nyameaama/Converse-Engine/Avionics/SubController Program.docx

DESIGN DOCUMENT

Area : Converse Engine

Category: Feed (Piping)

TEAM: Propulsion

Nyameaama Gambrah

Sub Controller Program

Sensor Calculation

Comm Module

ECU

SPI Interrupt

Telemetry Log

Handler

SBC Program Loop

Request

Permanent Storage

Update New Value

Remove Old Value

Value Table
