nyameaama/Converse-Engine/docs/tap-off description.docx

DESIGN DOCUMENT

Area : Converse Engine

Category: Feed (Piping)

TEAM: Propulsion

Nyameaama Gambrah

Tap-Off Description

Electrical

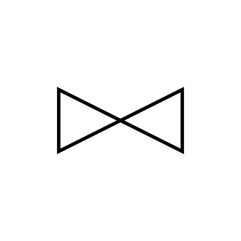
[picture p8: figure]
File:Valve.svg - Wikipedia

Tap-off propellant line

Initial Propellant Line

valve

valve

2-way pipe
