nyameaama/Converse-Engine/Avionics/Engine Startup-Shutdown (base).docx

Engine Startup (Base)

4

3

2

1

Checks

Fuel Pump Start

MOV Open

Fuel Pump Start

MFV Open

Start:

Engine Shutdown

Pumps Shutdown

Valves Close

Stop:
