nyameaama/Converse-Engine/docs/assets/rough sketches.docx

Combustion Chamber

Fuel propellant line

LOX propellant line

Injector Assembly

Engine Central Struct
