nyameaama/Converse-Engine/docs/Pressure_Fed/Engine Purge System - PF_Variant.docx

DESIGN DOCUMENT

Area : Converse Engine

Category: Feed (Purge)

TEAM: Propulsion

Nyameaama Gambrah

Engine Purge System

LOX Line

Fuel Line

C-Chamber

Electrical

Pressure loss

Valve

Pipe 2-Way

Nitrogen Gas
