nyameaama/Converse-Engine/docs/Electric_Feed/Engine Purge System-EF_Variant.docx

Engine Purge System

LOX Purge Pipe Vent

Fuel Purge Pipe Vent

C-Chamber

Valve

Post -Pump

Post -Pump

Fuel Pipe

Fuel Purge Pipe Vent

Electrical

LOX Pipe

Valve

Valve

Pre-Pump

Pre-Pump

Pressure loss

Valve

Pipe 2-Way

Nitrogen Gas

LOX Purge Pipe Vent
