nyameaama/Converse-Engine/Piping/Propellant Piping/Propellant Piping.docx

Propellant Piping

PUMP

PUMP

Inlet

Sensor Bridge

Sensor Bridge

Injector

Valve

Valve
