nyameaama/Converse-Engine/Avionics/SBControllerFirmware/PTDrivers/PT_SB-Program.docx

DESIGN DOCUMENT

Area : Converse Engine

Category: Feed (Piping)

TEAM: Propulsion

Nyameaama Gambrah

Pressure Transducer Sub Controller Program

READ IN

Controller Communication Module

ECU

Pressure Calculation

SPI Comm

GPIO

LOW

HIGH

Drivers

Digital Port
