nyameaama/Converse-Engine/Avionics/SBControllerFirmware/TCDrivers/TC_SB-Program.docx

DESIGN DOCUMENT

Area : Converse Engine

Category: Feed (Piping)

TEAM: Propulsion

Nyameaama Gambrah

Thermocouple Sub Controller Program

Digital Port

READ IN

Controller Communication Module

ECU

Temperature Calculation

SPI Comm

GPIO

LOW

HIGH

Drivers

Digital Port
