nyameaama/Converse-Engine/Avionics/SBControllerFirmware/ValveDrivers/ValveSB-Program.docx

DESIGN DOCUMENT

Area : Converse Engine

Category: Feed (Avionics)

TEAM: Propulsion

Nyameaama Gambrah

Valve Sub Controller Program

CLOSE

OPEN

Controller Communication Module

ECU

Valve State Assignment

SPI Comm

GPIO

LOW

HIGH

Drivers

Digital Port
