nyameaama/Converse-Engine/Piping/Electrical Piping/Scaled Circuit/PF_Variant/Scaled-Circuit_PF.docx

Valve Casing

Pipe-Gas (Fuel Purge)

Pipe-Gas (LOX Purge)

Power

VCC

GND

Thermocouple Casing

Signal-In

Pipe-Electrical

Pipe-Electrical

Relay Module

Nitrogen Gas

Pressure Transducer Casing

Oxidizer Inlet

Pressure Transducer Casing

Power

GND

VCC

Signal-In

Relay Module

3

Pipe-Electrical

Pipe-Electrical

Valve Casing

Valve Casing

3

Pipe-Propellant-Line

4

4

Power

GND

VCC

Signal-In

Relay Module

Pipe-Electrical

CLK

VCC

CS

DO

AD595 Thermocouple Amplifier

Thermocouple Casing

Pipe-Electrical

ECU Power Supply Assembly

VCC

Pipe-Electrical

CS

DO

CLK

ECU

AD595 Thermocouple Amplifier

Fuel Inlet

Pipe-Propellant-Line

Pressurizer
