nyameaama/Converse-Engine/Nozzle-CC/misc_docs/Ariel_TCA_Calculations.pdf

# Rocket Propulsion Laboratory: Ariel Thrust Chamber Assembly Calculations Draft

### M. Phalen, R. Libman, J. Villegas

### March 5, 2017

Chief Engineer | Date

Abstract

This document covers the design of the combustion chamber and nozzle of RPL’s 500lbf methalox engine, Ariel, with an 80% bell nozzle approximation. Note: Gas Pressures are reported in atmospheres for easy comparison to curves sourced from braeunig.com. Future iterations of this document will be translated to English units as is common in for aerospace literature.

Nomenclature
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
m˙ F
m˙ O

= Chamber Area (in²
)
= Nozzle Exit Area (in²
)
= Nozzle Throat Area (in²
)
= Chamber Diameter (in)
= Nozzle Exit Diameter (in) = Nozzle Throat Diameter (in) = Characteristic Velocity ( f t
s

)
= Thrust Coefficient (unitless)
= Characteristic Length (in) = Length necessary for complete combustion. = Chamber Length (in)
= Thurst (lbf )
= Factor of Safety (Unitless)
= Gravity of Earth ( f t
s

2 )
= Specific Impulse (s)
= Ambient Pressure (atm)
= Chamber Pressure, (atm)
= Exit Pressure (atm)
= Nozzle Throat Pressure, (atm)
= Universal Gas Constant, ( lb∗lbf
◦R∗lb−mol)
= Yield Stress of Chamber Lining (psi) = Chamber Temperature (◦R)
= Nozzle Throat Temperature (◦R)
= Chamber Wall Thickness (in)
= Chamber Volume (in³
)
= Propellant Mass Flow Rate (lb
s

)
= Fuel Mass Flow Rate (lb
s

)
= Oxidizer Mass Flow Rate(lb
s

)
Mr
Mw
c
e
γ

= Mixture Ratio (unitless)
= Molecular Weight of the Exhaust (amu)
= Contraction Area Ratio (unitless)
= Expansion Area Ratio (unitless)
= Adiabatic Index-Ratio of Specific Heats (unitless)

Constants

FoS
ge
Pa
R
Sy

= 1.4
= 32.1740 f t
s

2
= 1 atm
= 1545.348963 lb∗lbf ◦R∗lb−mol

= 80000 psi

## 1 Introduction

Compared to other traditional rocket propellants, LOX and liquid CH4 is advantageous for deep space missions for several reasons. While it has a lower specific vacuum impulse than LOX/LH2, it presents other favorable properties such as a higher boiling point. This requires a less severe temperature differential to be maintained, reducing the risk of boil off. Methalox’s density is also significantly higher than LOX/LH2, allowing for smaller-less massive-propellant tanks. Further more, the propellant required for an additional trip(s) from an carbon dioxide rich atmosphere can be produced on-site with a small amount of seed hydrogen, allowing for considerable weight-propellant savings important for mission design. Here the Rocket Propulsion Laboratory goes through the initial design of a 2000 lbf methalox engine, dubbed Ariel.

## 2 Approach

To ensure accuracy and reliability in the calculations, several reference texts were used to baseline the design. In particular, Modern Engineering for Design of Liquid-Propellant Engines by Dieter K. Huzel and David H. Huang and Rocket Propulsion Elements, 8

th Ed.
by George P. Sutton were heavily referenced to bridge the knowledge gap and guide the designs of the combustion chamber and the nozzle.
Both texts show that the overall design of a given thrust chamber assembly is character-ized by the desired propellant, chamber pressure, exit pressure, thrust, and nozzle contour for a given engine. From a given propellant and chamber pressure, key parameters of the engine’s exhaust can be computed. In particular they are: the adiabatic index, adiabatic flame temperature, molecular weight of the exit gas, and the optimum mixture ratio of the propellant. However neither text goes into detail about characterizing the chemical properties of propellants. For this, software like Stanford’s StanJan and NASA’s CEA application are used. braeunig.us hosts the relevant curves for methalox, calculated with StanJan . This data was cross checked with CEAweb to verify accuracy.

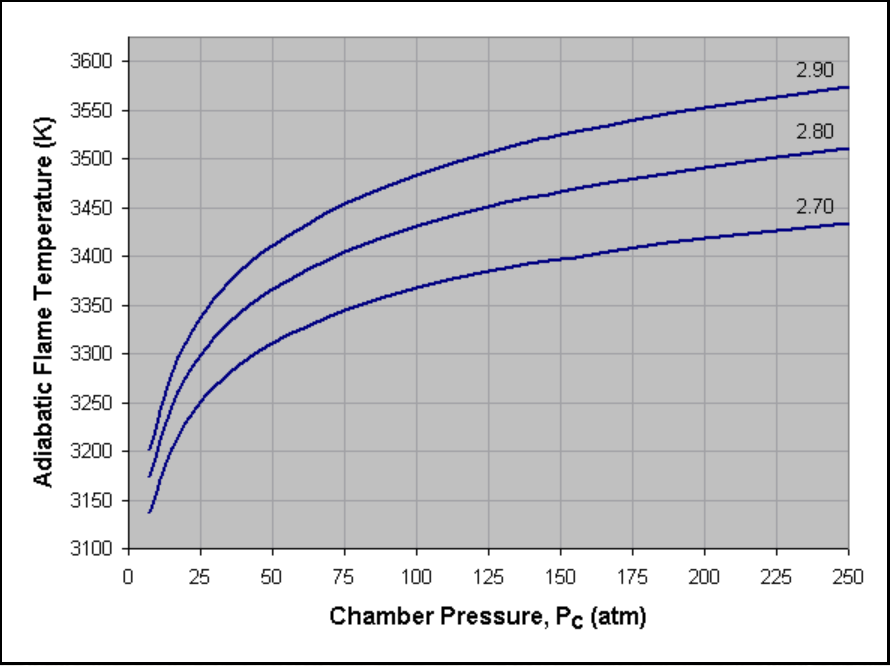
[picture p12: figure]
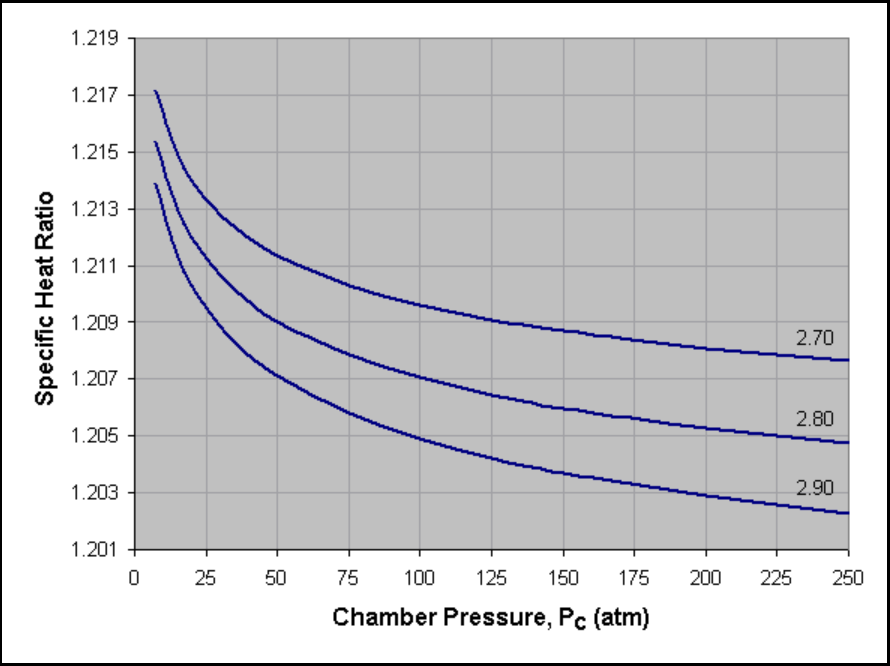
[picture p13: figure]
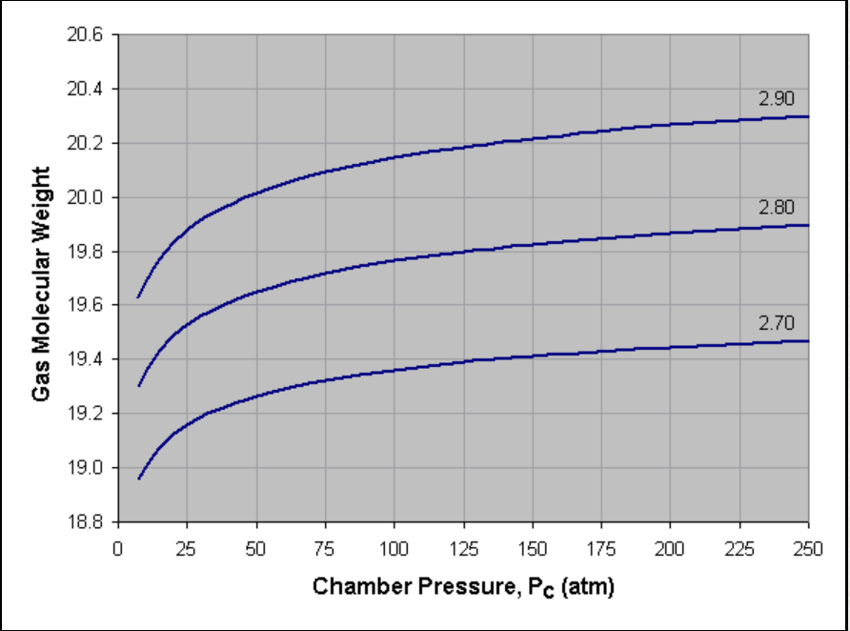
[picture p14: figure]

(a) Adiabatic Flame Temp. | (b) Molecular Weight of Gas | (c) Specific Heat Ratio

Figure 1: Three Data-sets in Reference

Determining the optimum mixture ratio requires that Specific Impulse vs Mixture Ratio curves be calculated, holding Chamber Pressure constant. The global maxima for these curves provide the optimal mixture ratio for a given pressure. This is shown in another graph from braeunig.us , where they have graphed Optimal Mixture Ratio vs Pressure, holding Exit Pressure constant:

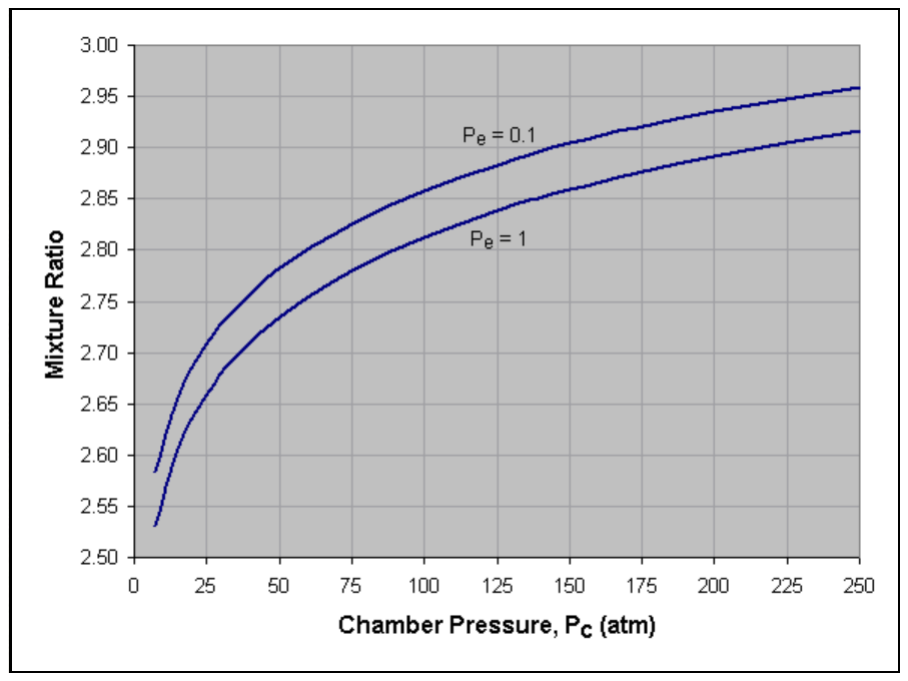
[picture p15: figure]

Figure 2: MR versus Pc

### 2.1 Thrust

The desired thrust acts as an indirect scaling factor for the engine, influencing the diameter of the chamber and diameter of the nozzle’s exit relative to the diameter of the nozzle’s throat. With this in mind, Ariel was designed to produce only 500lbf as this would reduce the cost in both materials and time to produce as well as mitigate risks that would scale with the engine size.

### 2.2 Nozzle Contour

The nozzle follows suit in that an an 80% bell nozzle approximation is used as it provides a reasonable trade off between performance and weight. Furthermore, considering how thor-oughly bell nozzles have been studied and documented, they are a safe choice for RPL’s first attempt at constructing a liquid rocket engine.

### 2.3 Exit Pressure

As [citation needed, Huzel+Huang] explains, having an exit pressure different from the ambient pressure results in over or under expansion of the exhaust which are both unfavorable. Ariel was designed to be fired at sea level, so the desired Exit Pressure was defined as one atm.

### 2.4 Chamber Pressure

Looking at Figure 1 and Figure 2 and Equations ?? and ??, it’s apparent that a higher chamber pressure and corresponding mixture ratio would result in higher specific impulse. However, given that Ariel will be a small motor and a first for RPL, high pressures were considered an unnecessary safety risk. At the other end of the spectrum, while lowering chamber pressure mitigates pressure related hazards, minor fluctuations in the mixture ratio would result in increasing large perturbations of chamber pressure. With this in mind, looking at Figure 2 it can be seen that a reasonable range for chamber pressure is 50 to 90 atmospheres.
Ariel was designed to have a chamber pressure of 68 atmospheres. 68 is a conservative average, it falls in the middle of the above range but leans slightly towards the lower end.

### 2.5 Exhaust Properties

With the characteristic engine parameters defined, exhaust properties can discerned from the data generated from StanJan or CEAweb.

## 3 Calculations

### 3.1 Characteristic Engine Parameters

Having defined the independent characteristic parameters for Ariel’s combustion chamber the optimal mixture ratio of methalox to feed the engine was approximated by examining Figure 2. Using these values for thrust, chamber pressure, exit pressure, and the mixture ratio the exhaust parameters where calculated with CEAweb ??

Characteristic Engine Parameters F
Pc
Pe
Tc
Mr
Mw
γ

= 2000 lbf
= 68 atm (999.321 psi)
= 1 atm (14.6959 psi)
= 6051.60 ◦R
= 2.77
= 20.158 amu
= 1.2161

### 3.2 Area Contraction and Expansion Ratios, c and e

c =

Ac
At

= 1.317303 +

32346880 − 1.317303
1 + ( Dt
1.041567∗10⁻¹⁰ )
0.6774809 = 6.0510 | (1)

This equation for the contraction area ratio comes from a rough fitting of Figure 4-9 from Huzel and Huang .

e =

Ae
At

=

(

2
γ+1 )

1
γ−1 (

Pc
Pe

)

1
γ

[( γ+1
γ−1

)[1 − (

Pe
Pc

)

γ−1
γ ]] ¹
2
= 8.5917 | (2)

### 3.3 Thrust-Chamber Performance Parameters

### 3.3.1 Characteristic Velocity, c∗

c

∗ =

√
geγRTc

γ

rh
2

γ+1 i γ+1
γ−1

= 5929

f t
s

(3)

Characteristic Velocity is a measure of the combustion performance, similar to Specific Impulse.

### 3.3.2 Thrust Coefficient, Cf

Cf = λ ∗

### vuut

2γ

2
γ − 1
2

γ + 1 γ+1
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
Pe − Pa
Pc
= 1.5640 | (4)

Where λ = .985 is the correction factor associated with a 80% bell nozzle for an engine of this size . It applies only to the momentum term of Cf as it accounts for divergence from uniform axial flow (the contour of the nozzle at it’s exit isn’t parallel to the central axis of the thrust chamber).

### 3.3.3 Specific Impulse, Isp

Isp =

c

∗Cf
ge
= 288s | (5)

Specific Impulse is the amount of thrust generated per unit of propellant, or, in essence, the performance of our engine.

### 3.4 Mass Flow, m˙

The Propellant Mass Flow Rate

m˙ =

F

Isp

= 6.9394

lb
s

(6)

the Fuel Mass Flow Rate,

m˙ F =

m˙
r + 1

= 1.841

lb
s

and the Oxygen Mass Flow Rate.

m˙ O =

r ∗ w˙
r + 1

= 5.099

lb
s

### 3.5 Nozzle Throat Parameters

Nozzle Throat Temperature,

Tt = Tc

2
1 + γ
= 5461.5
◦R | (7)

Nozzle Throat Pressure,

Pt = Pc

γ + 1
2

−γ
γ−1
= 38.173atm | (8)

Nozzle Throat Area,

At =

mI ˙ sp
PcCf

= 1.2796in²
(9)

and Nozzle Throat Diameter.

Dt =

4At
π

1
2
= 1.2764in | (10)

Nozzle Exit Area,

Ae = eAt = 10.9942in²
(11)

and Nozzle Exit Diameter.

De =

4Ae
π

1
2
= 3.7414in | (12)

### 3.6 Chamber Dimensions

a) Calculate the Chamber Volume.

Vc = AtL

∗ = 51.1848in³
(13)

L

∗ = 40in

Characteristic Lengths and Volumes are a more intuitive way to express the requirements for efficient combustion of the propellant, which is usally expressed as propellant stay time (τ ). Characteristic Length is proportional to the complexity molecules that make up the propellant; examining table from Huzel and Huang, it can be reasoned Methalox will have a characteristic length between that of RP-1 and LOX+LH2. This is estimated to be 40 in.
b) Calculate the Chamber Length by utilizing the contraction ratio (c) to solve
for Ac, and thus Dc.

Vc = (1.1)Ac ∗ Lc = 51.1848in³ (14)

Chamber Area
Ac = cAt = 7.7429in²
(15)

Chamber Diameter

Dc = (⁴Ac
π

)

1
2 = 3.1398in | (16)

Chamber Length

Lc =

Vc
1.1Ac
= 6.0096in | (17)
c) Chamber Wall Thickness

From Barlow’s law relating the maximum working pressure to a pipe’s geometry:

FoS ∗ Pc =

2 ∗ Sy ∗ tw

Doutside

(18)

Where Doutside = Dc + 2tw

We derived the equation that gives the desired thickness of the chamber lining

tw =

FoS ∗ Pc ∗ Dc
2 ∗ Sy − 2 ∗ FoS ∗ Pc
= 0.0279in | (19)

Sy equals the yield stress of material used for the chamber lining; for Ariel that

material is Inconel 718, with a yield stress of 80000 psi

### 3.7 Nozzle Contour

Most references suggest using a parabolic approximation for bell nozzles . However, the examples provided in Huzel and Huang couldn’t be reconciled with the data they provided. A lecture from Georgia Tech suggested to use the general conic equation to approximate the contour of a bell nozzle. This follows the form:

y = P ∗ x + Q + (S ∗ x + T)

1
2 | (20)

## 4 Results

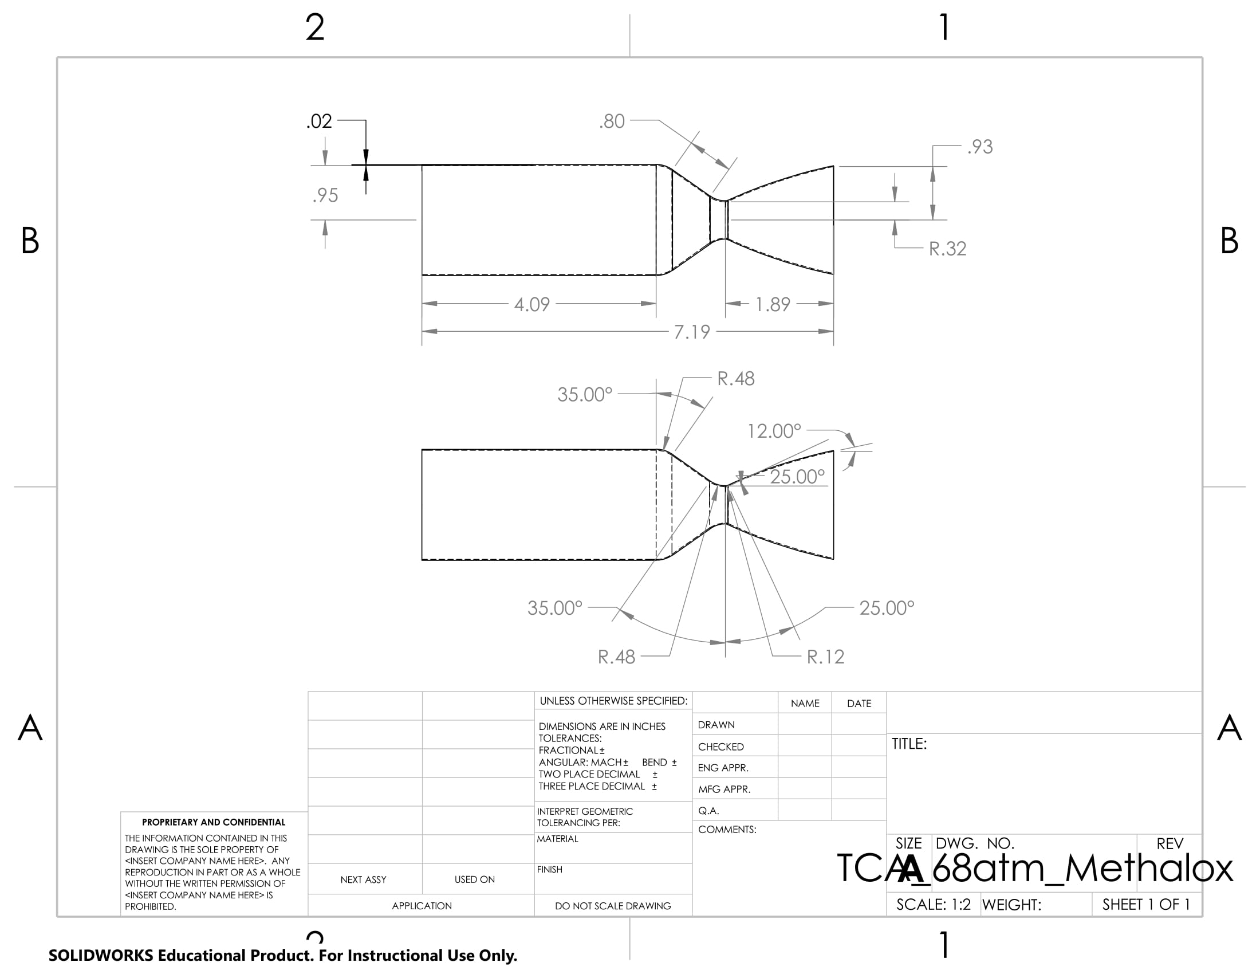
[picture p16: figure]

Figure 3: Current Model

## 5 Conclusions

In order to bridge the knowledge gap between professional industry knowledge and collegiate student knowledge, we have heavily utilized the information from Modern Engineering for Design of Liquid-Propellant Engines by Dieter K. Huzel and David H. Huang as well as Rocket Propulsion Elements, 8th Ed. by George P. Sutton . This literature provided us with the equations necessary to design and model the first iteration of Ariel. Further iteration will be guided by results from analysis, as an example, CFD can be used to test the approximation made for c.
