nyameaama/Converse-Engine/docs/PLACEMENT.docx

DESIGN DOCUMENT

Area : Converse Engine

Category: Feed (Struct)

TEAM: Propulsion

Nyameaama Gambrah

COMPONENT PLACEMENT

Face 2

Face 4

Face 3

Face 1

s

Faces = 4
