nyameaama/Converse-Engine/Avionics/Peripheral Controllers Abstract.docx

DESIGN DOCUMENT

Area : Converse Engine

Category: Feed (Avionics)

TEAM: Propulsion

Nyameaama Gambrah
