nyameaama/Converse-Engine/Nozzle-CC/igniter/Igniter (Abstracted).docx

Igniter (Abstracted)

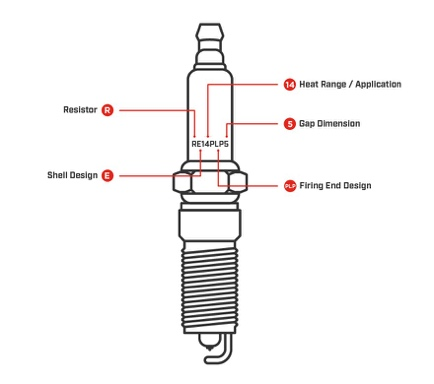
[picture p17: figure]
What are the parts of a spark plug called? | Champion Auto Parts

Spark Plug
