nyameaama/Converse-Engine/Avionics/Casings/EngineControlUnit/ECU/ECU-Casing.png

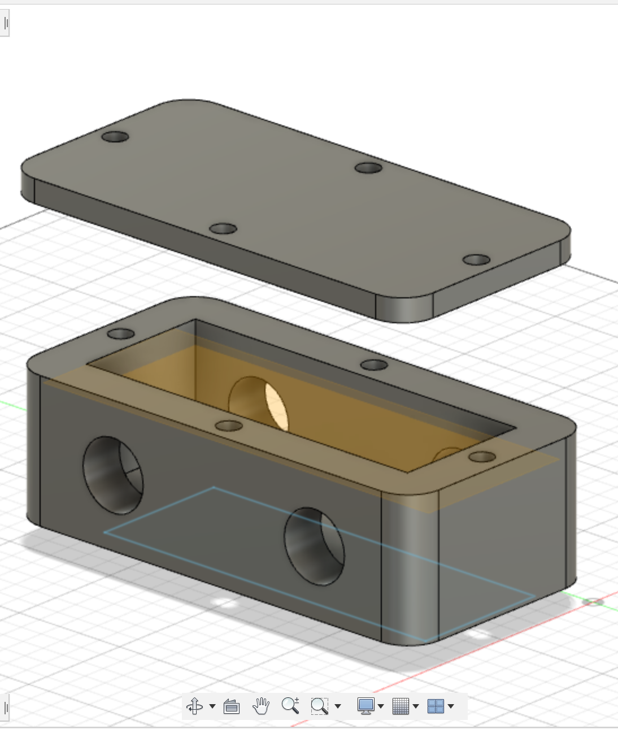
Avionics/Casings/EngineControlUnit/ECU/ECU-Casing.png
