nyameaama/Converse-Engine/Nozzle-CC/injector/injector-assembly.png

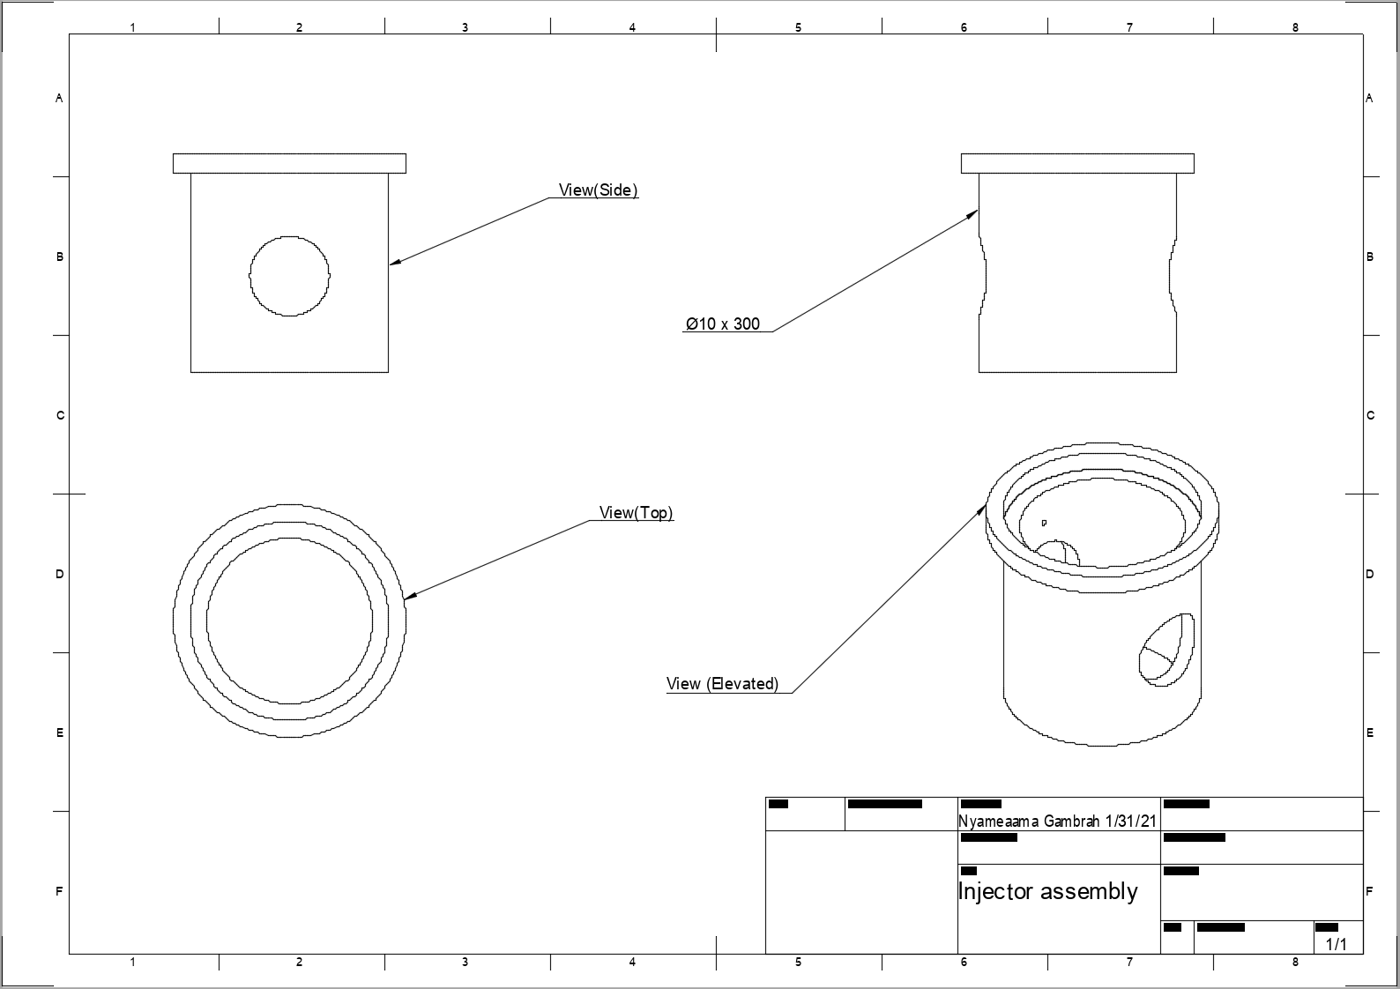
Nozzle-CC/injector/injector-assembly.png
