nyameaama/Converse-Engine/docs/Controller-Power-Assemblies/measure-1.png

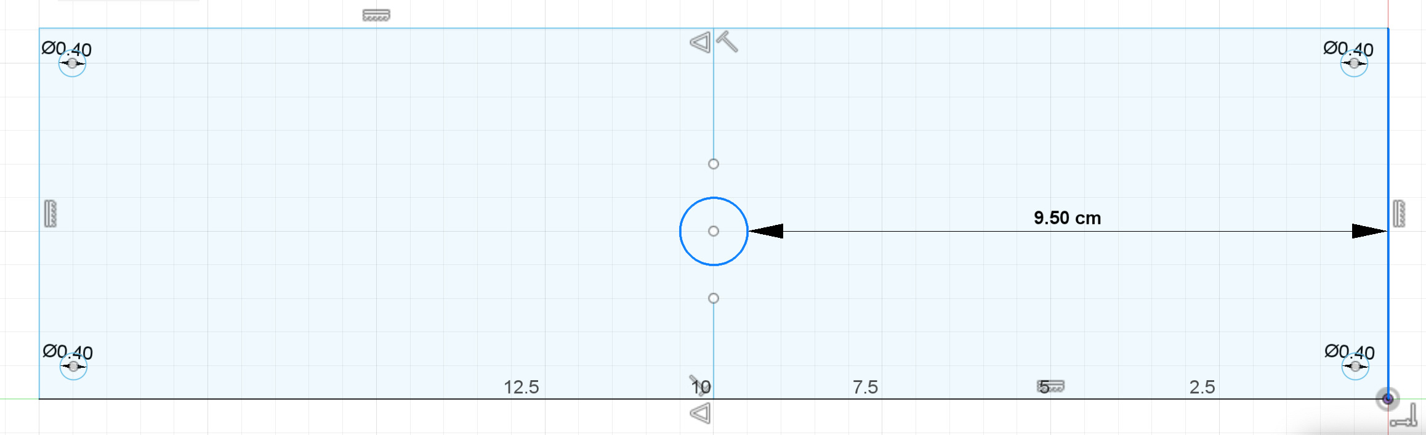
docs/Controller-Power-Assemblies/measure-1.png
