nyameaama/Converse-Engine/docs/Testing-terminal-controller/Casing/arduino-uno-in-fusion-360-format-1/Capture.PNG

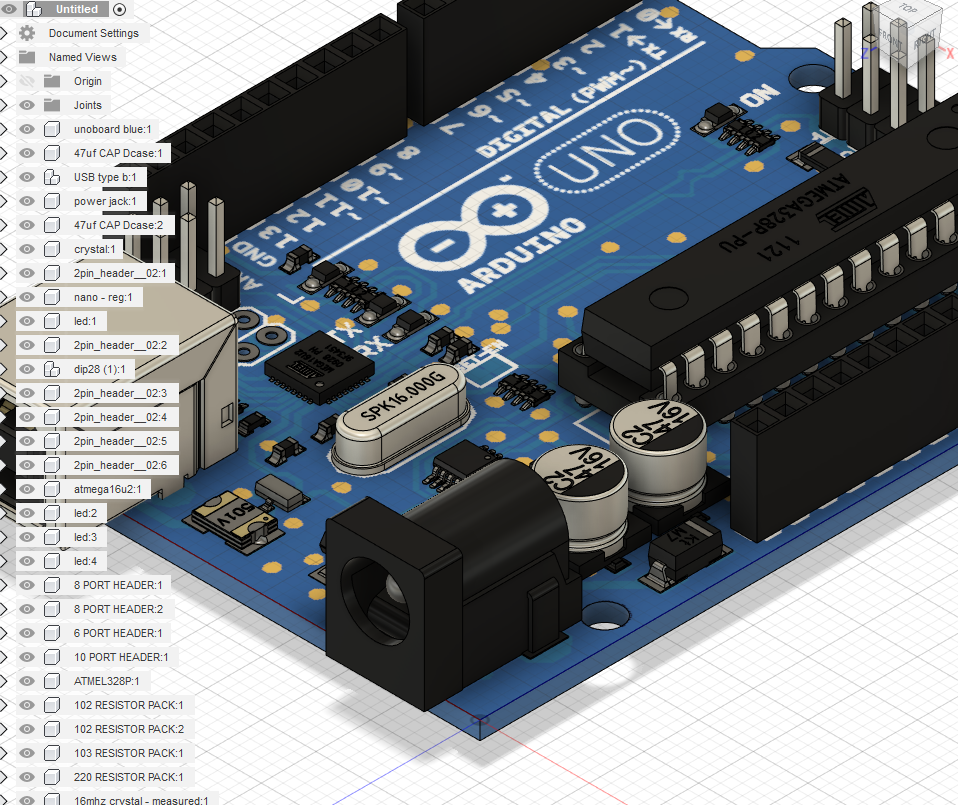
docs/Testing-terminal-controller/Casing/arduino-uno-in-fusion-360-format-1/Capture.PNG
