nyameaama/Converse-Engine/docs/Testing-terminal-controller/Casing/arduino-uno-in-fusion-360-format-1/raas-rendering20150623-6149-15dbs3x.jpg

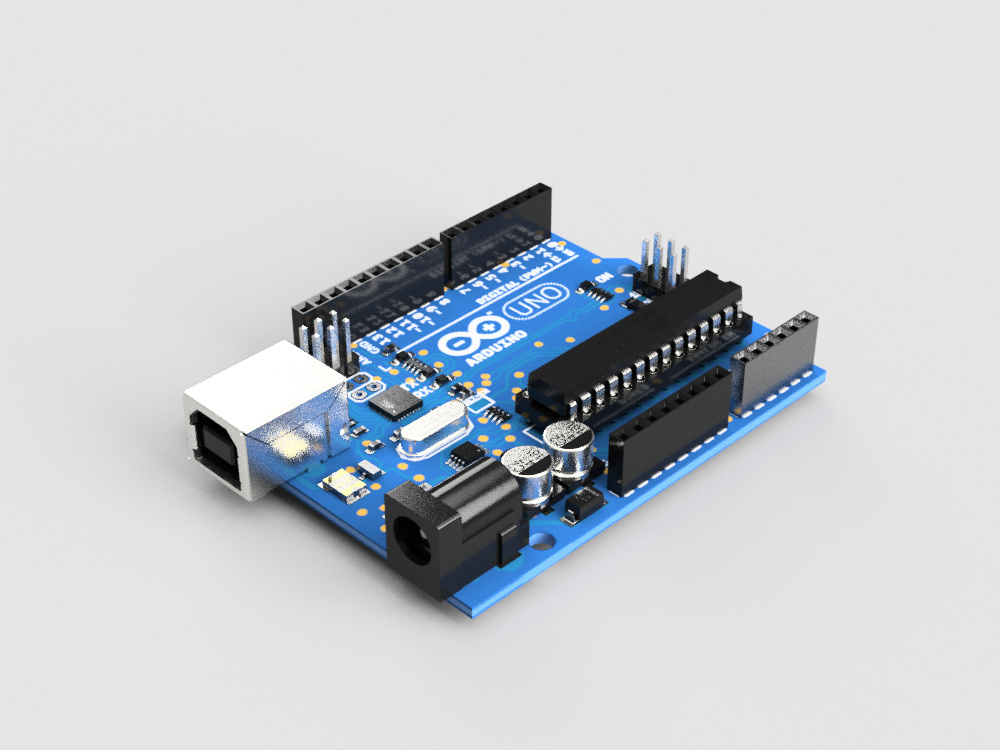
docs/Testing-terminal-controller/Casing/arduino-uno-in-fusion-360-format-1/raas-rendering20150623-6149-15dbs3x.jpg
