nyameaama/Converse-Engine/Avionics/ECU Program Chart.pdf

## DESIGN DOCUMENT

Area : Converse Engine
Category: Feed (Avionics)

TEAM: Propulsion
Nyameaama Gambrah

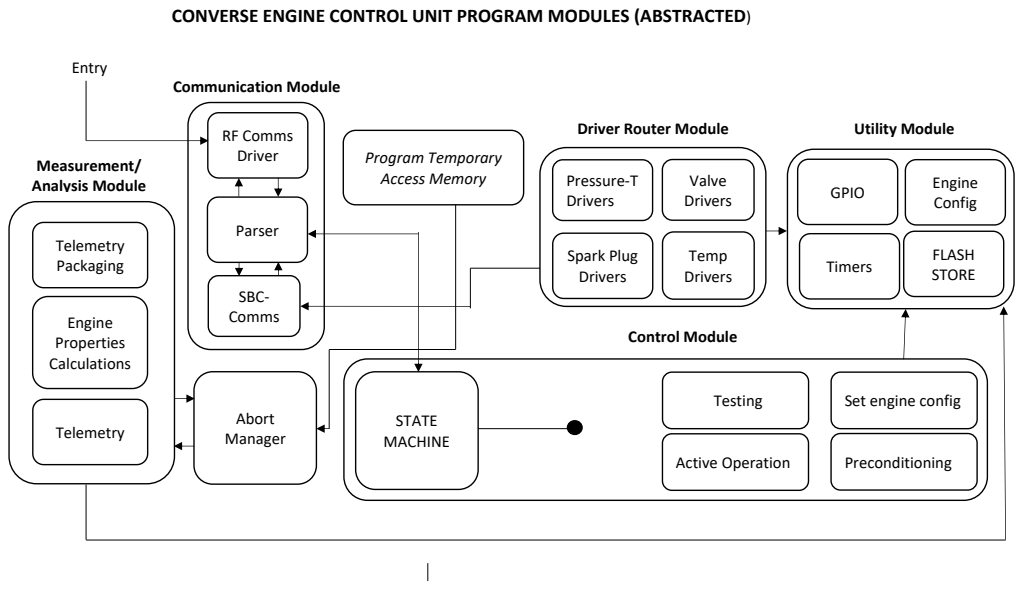
[picture p33: page 2]
Valve Drivers; Measurement/ Analysis Module; Entry; Abort Manager; Pressure-T Drivers; Temp Drivers; SBC- Comms; Spark Plug Drivers; Program Temporary Access Memory; Telemetry Packaging; Engine Properties Calculations; Telemetry; GPIO; Timers; FLASH STORE; RF Comms Driver; Engine Config; Utility Module; Control Module; Preconditioning; Parser; STATE MACHINE; Active Operation; Testing; Communication Module

CONVERSE ENGINE CONTROL UNIT PROGRAM MODULES (ABSTRACTED)

Driver Router Module

Set engine config
