nyameaama/Converse-Engine/Avionics/SubController Program.pdf

## DESIGN DOCUMENT

Area : Converse Engine
Category: Feed (Piping)

TEAM: Propulsion
Nyameaama Gambrah

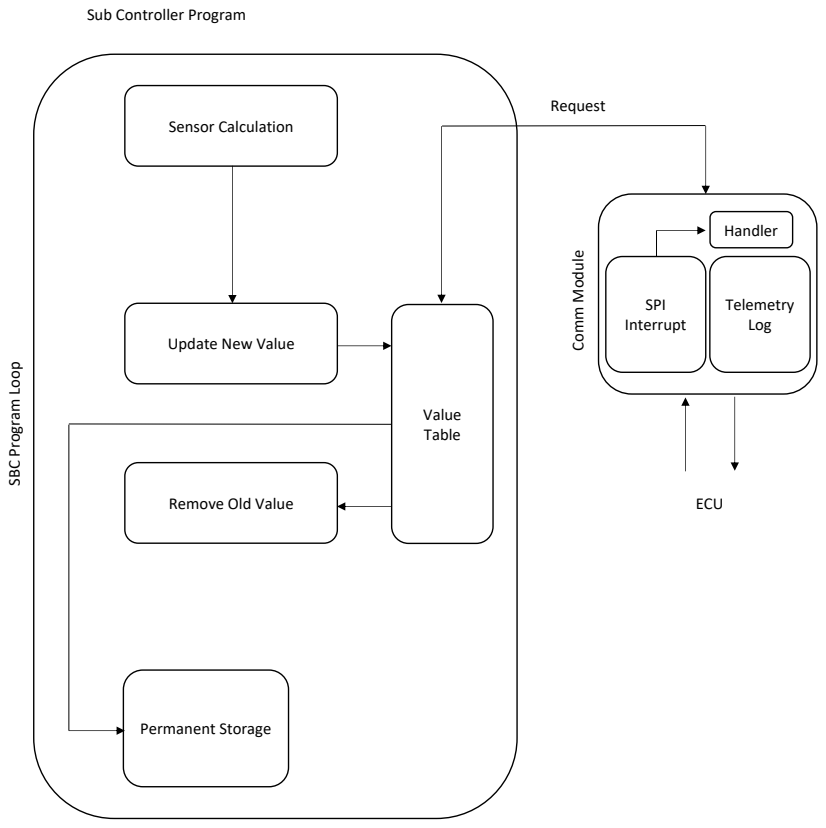
[picture p34: page 2]
SPI Interrupt; Sensor Calculation; Value Table; Permanent Storage; Handler; Request; ECU; Telemetry Log; Comm Module

Sub Controller Program

Update New Value

SBC Program Loop

Remove Old Value
