nyameaama/Converse-Engine/docs/Pressure_Fed/Engine Abstracted-PF_Variant.pdf

## DESIGN DOCUMENT

Area : Converse Engine
Category: Feed (Piping)

TEAM: Propulsion
Nyameaama Gambrah

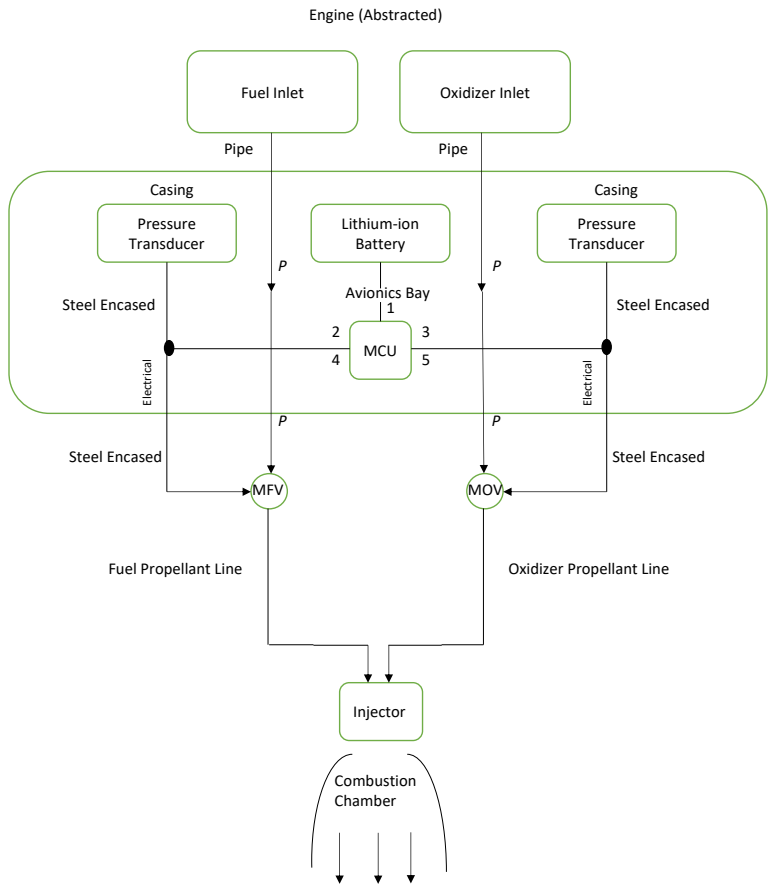
[picture p35: page 2]
Engine (Abstracted); Fuel Inlet; Oxidizer Inlet; Avionics Bay; Pipe; Pressure Transducer; MCU; Casing; Steel Encased; Lithium-ion Battery; MFV; MOV; Injector; Combustion Chamber; Fuel Propellant Line; Oxidizer Propellant Line; Electrical
