nyameaama/Converse-Engine/docs/Electric_Feed/Engine Abstracted-EF_Variant.pdf

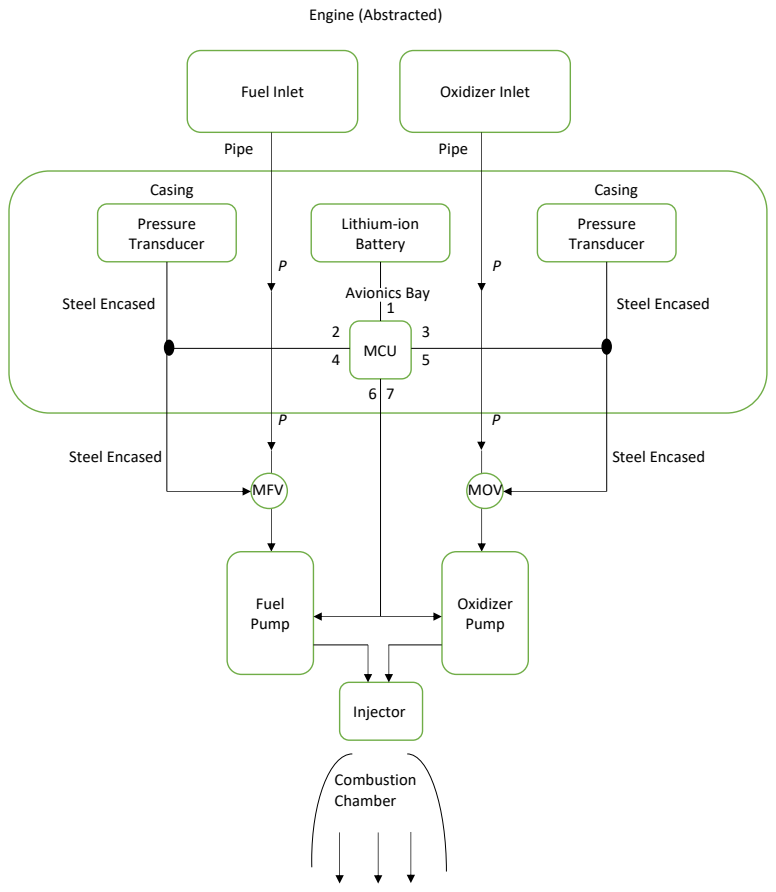
[picture p36: page 1]
Engine (Abstracted); Fuel Inlet; Oxidizer Inlet; Avionics Bay; Pipe; Pressure Transducer; MCU; Casing; Steel Encased; Lithium-ion Battery; MFV; MOV; Fuel Pump; Oxidizer Pump; Injector; Combustion Chamber
