nyameaama/Converse-Engine/Piping/Electrical Piping/Scaled Circuit/PF_Variant/Scaled-Circuit_PF.pdf

# Fuel Inlet

# Oxidizer

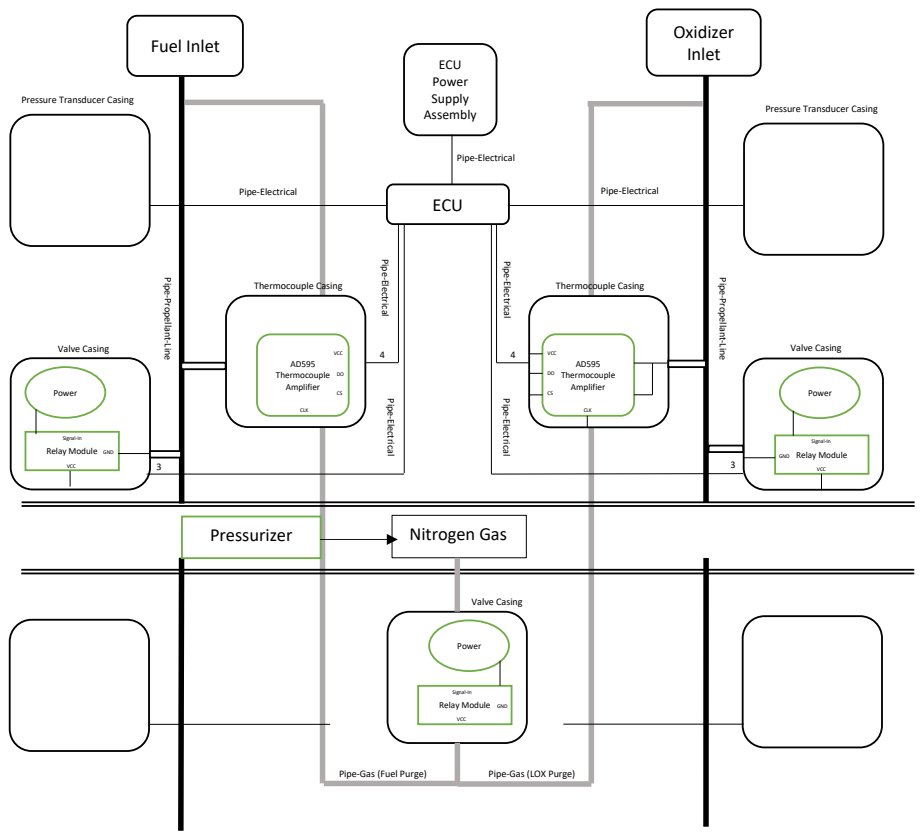
[picture p37: page 1]
Inlet; ECU; ECU Power Supply Assembly; AD595 Thermocouple Amplifier; CLK; Pipe-Electrical; VCC; Thermocouple Casing; Relay Module; Signal-In; GND; Power; 4 Pipe-Electrical; Valve Casing; 3 VCC; Nitrogen Gas; Pipe-Gas (Fuel Purge); Pipe-Gas (LOX Purge); Pressurizer

Pressure Transducer Casing

Pipe-Propellant-Line
