nyameaama/Converse-Engine/Piping/Electrical Piping/Scaled Circuit/EF_Variant (Discontinued)/Scaled-Circuit_EF.pdf

# Fuel Inlet

# Oxidizer

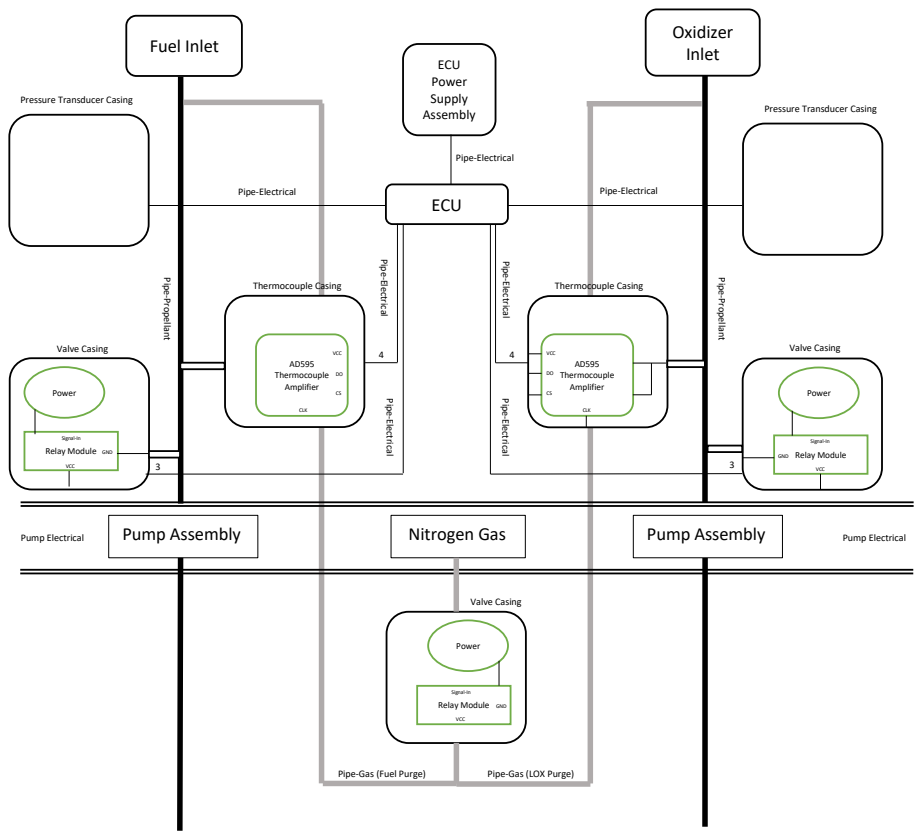
[picture p38: page 1]
Inlet; ECU; ECU Power Supply Assembly; AD595 Thermocouple Amplifier; CLK; Pipe-Electrical; VCC; Thermocouple Casing; Relay Module; Signal-In; GND; Power; 4 Pipe-Electrical; Pipe-Propellant; Valve Casing; 3 VCC; Pump Electrical; Pump Assembly; Nitrogen Gas; Pipe-Gas (Fuel Purge); Pipe-Gas (LOX Purge)

Pressure Transducer Casing
